jygnw29kms-bit/135er-Universal-Helicopter-Controller/cad/validation/src/validation_plate_01.scad

use <fit_coupons.scad>
translate([0,0,0]) tube_coupon();
translate([10,46,0]) shaft_coupon();
translate([10,103,0]) bearing_coupon();
translate([135,0,0]) magnet_coupon();
translate([137,40,0]) fastener_coupon();
